emeb/ch32v003_lcd_nav/firmware/test/funconfig.h

#ifndef _FUNCONFIG_H
#define _FUNCONFIG_H

#define FUNCONF_SYSTICK_USE_HCLK 1
#define FUNCONF_USE_HS1 1               // Use Internal Oscillator
#define FUNCONF_USE_UARTPRINTF  0
//#define FUNCONF_USE_DEBUGPRINTF 0
#define FUNCONF_USE_DEBUGPRINTF 1
//#define FUNCONF_NULL_PRINTF 1

#define CH32V003        1

#endif
